its-kronos/The-Breadboard/Kicad/Breadboard.kicad_sch

## KiCad design Kicad/Breadboard.kicad_sch (2025-06-30)

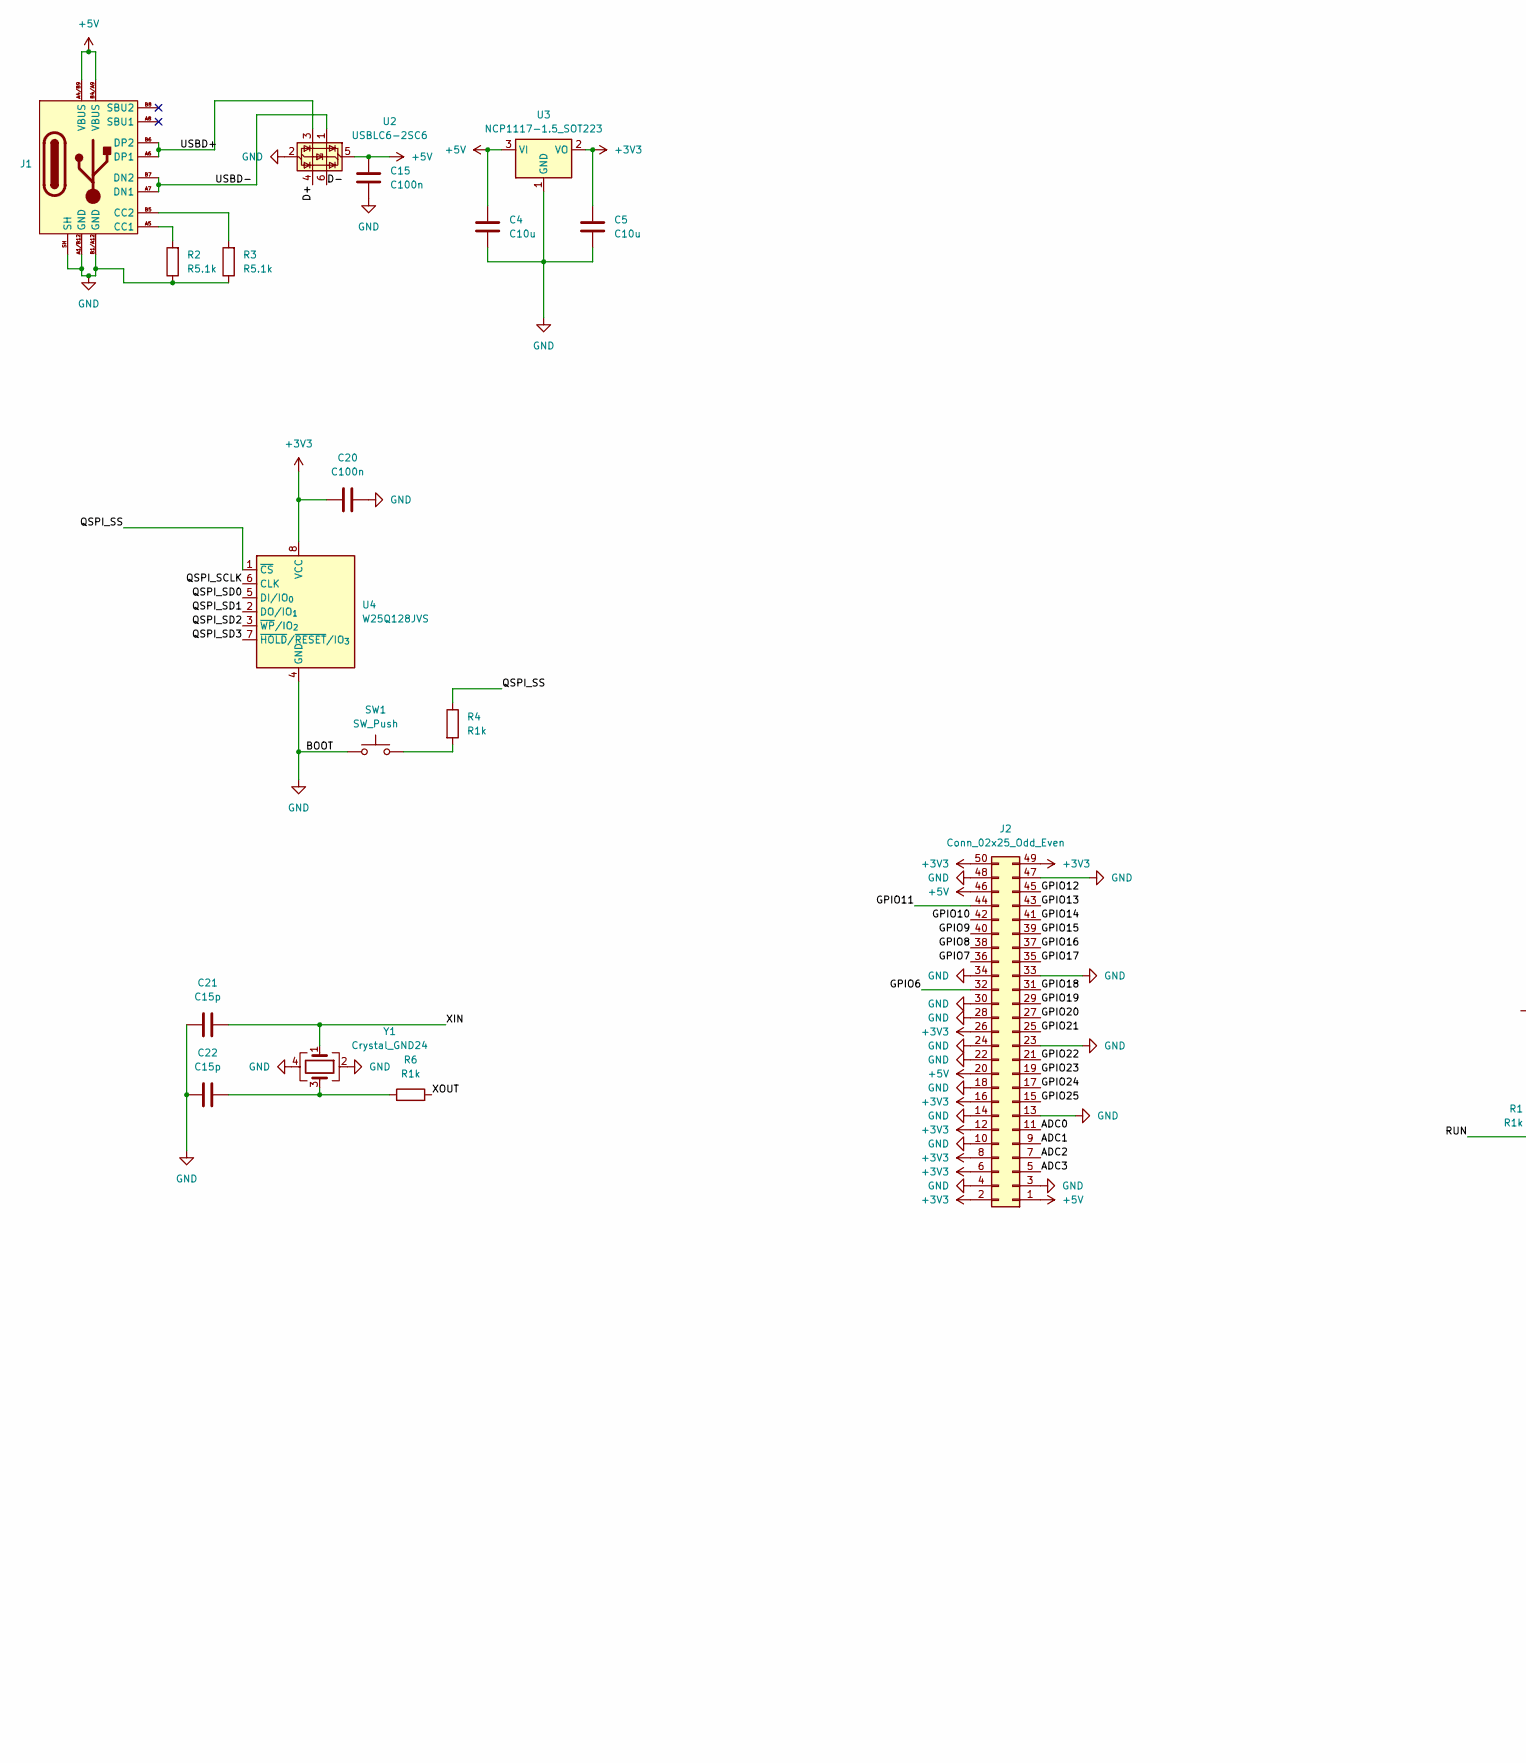
[picture p2: schematic Breadboard.kicad_sch, part in row 1, column 1]

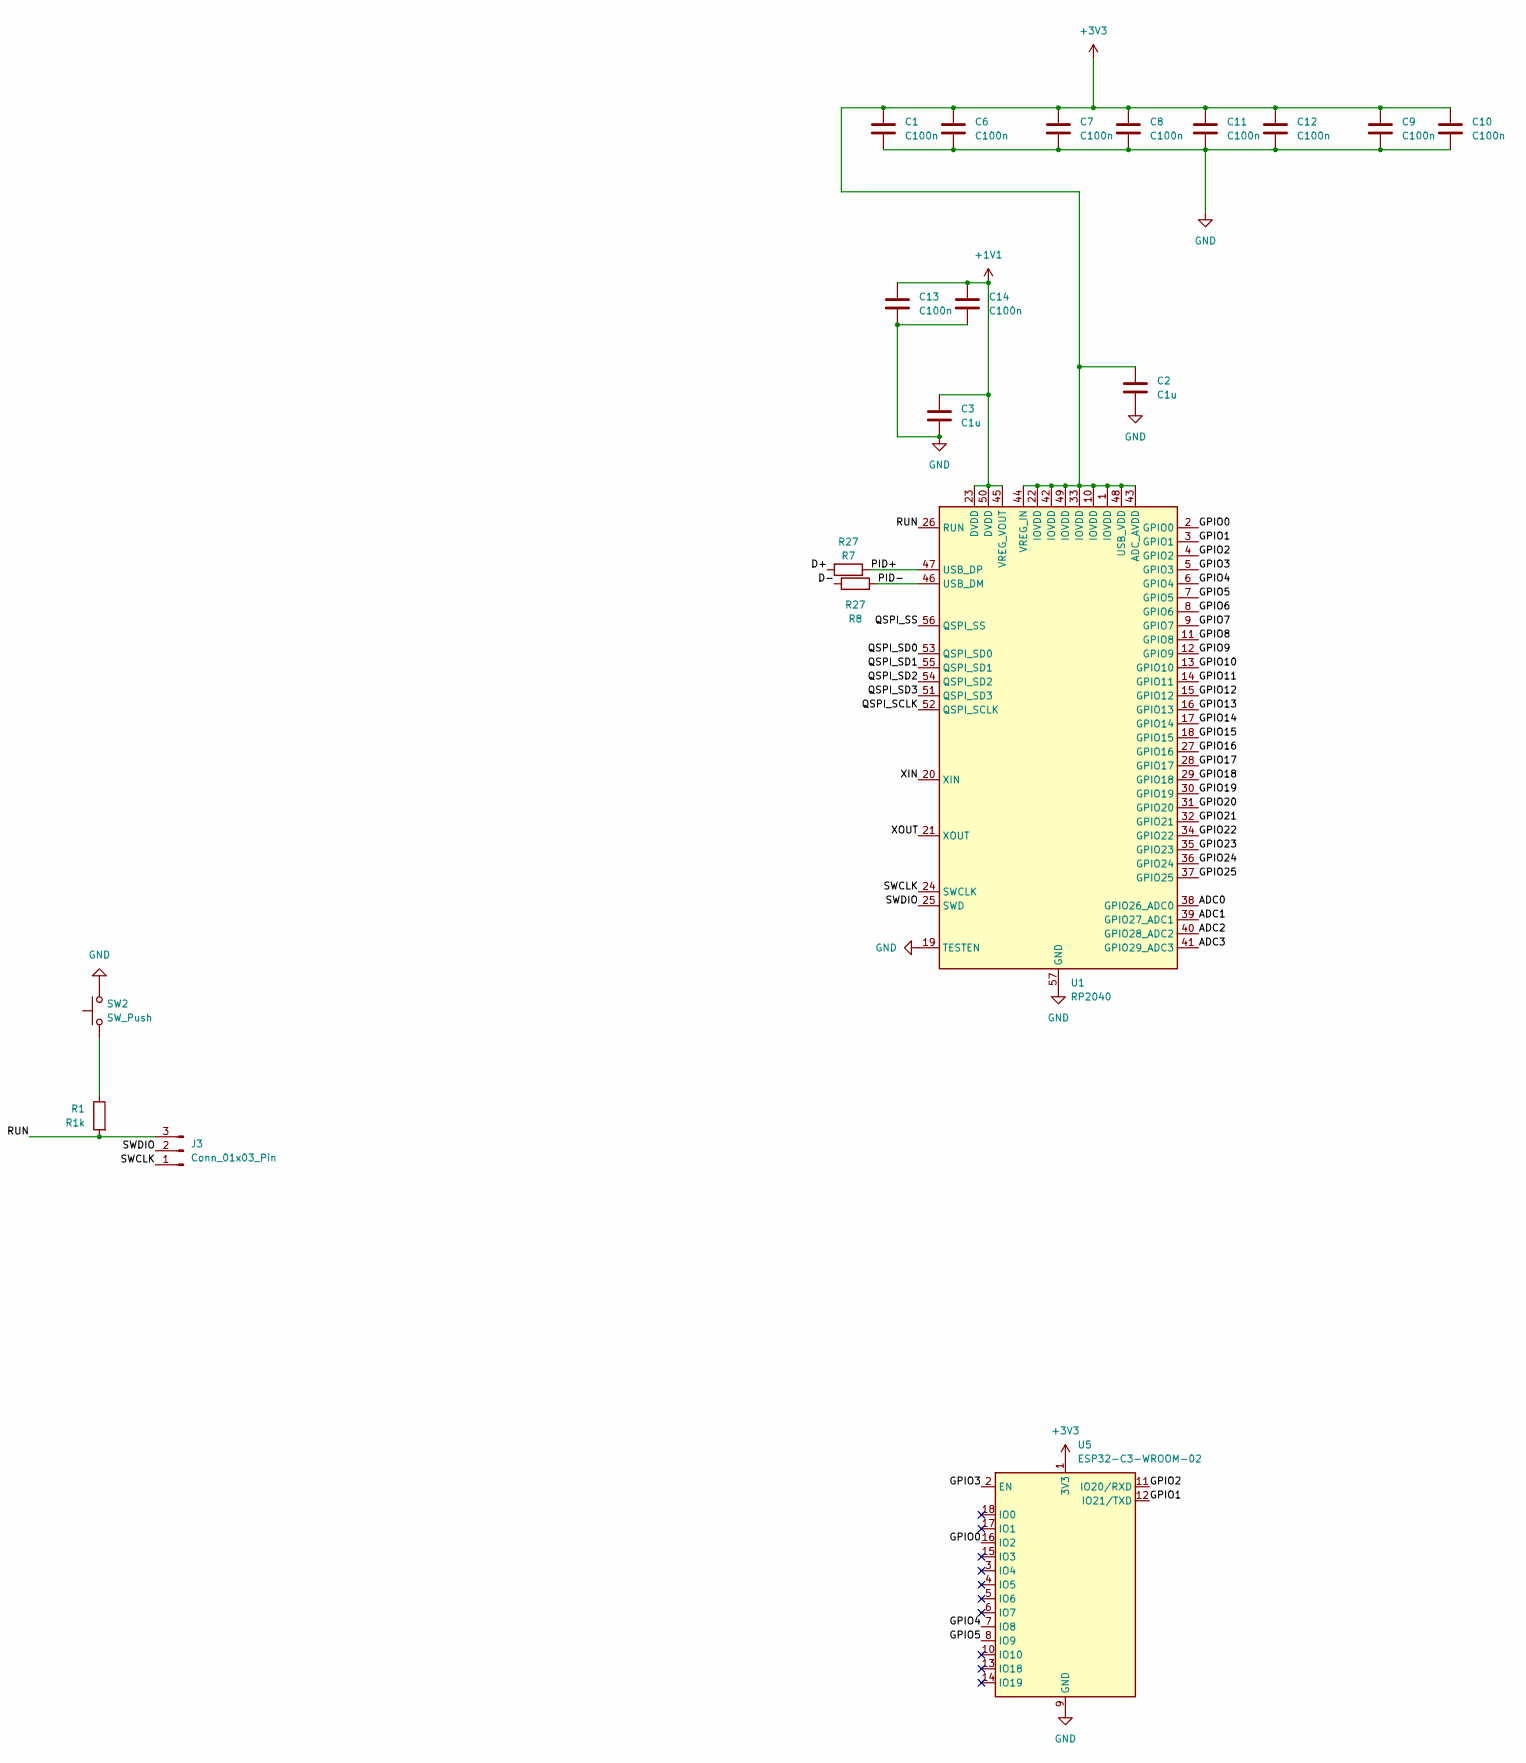
[picture p3: schematic Breadboard.kicad_sch, part in row 1, column 2]

Parts:
C1, C6, C7, C8, C9, C10, C11, C12, C13, C14, C15, C20: C100n; C_0402_1005Metric
C2, C3: C1u; C_0402_1005Metric
C4, C5: C10u; C_0402_1005Metric
C21, C22: C15p; C_0402_1005Metric
J1: Korean Hroparts Elec - Type C 31 M 12 - 16P - USB 2.0
J2: Conn_02x25_Odd_Even; PinHeader_2x25_P1.00mm_Vertical
J3: Conn_01x03_Pin; PinHeader_1x03_P1.00mm_Vertical
R1, R4, R6: R1k; R_0402_1005Metric
R2, R3: R5.1k; R_0402_1005Metric
R7, R8: R27; R_0603_1608Metric
SW1, SW2: SW_Push; SW_PUSH_6mm
U1: RP2040; QFN-56-1EP_7x7mm_P0.4mm_EP3.2x3.2mm
U2: USBLC6-2SC6; SOT-23-6
U3: NCP1117-1.5_SOT223; SOT-223-3_TabPin2
U4: W25Q128JVS; SOIC-8_5.3x5.3mm_P1.27mm
U5: ESP32-C3-WROOM-02
Y1: Crystal_GND24; Crystal_SMD_3225-4Pin_3.2x2.5mm

Connections:
+1V1: C3.1, C13.1, C14.1, U1.23 (DVDD), U1.45 (VREG_VOUT), U1.50 (DVDD)
+3V3: C1.1, C2.1, C5.1, C6.1, C7.1, C8.1, C9.1, C10.1, C11.1, C12.1, C20.1, J2.2, J2.6, J2.8, J2.12, J2.16, J2.26, J2.49, J2.50, U1.1 (IOVDD), U1.10 (IOVDD), U1.22 (IOVDD), U1.33 (IOVDD), U1.42 (IOVDD), U1.43 (ADC_AVDD), U1.44 (VREG_IN), U1.48 (USB_VDD), U1.49 (IOVDD), U3.2 (VO), U4.8 (VCC), U5.1 (3V3)
+5V: C4.1, C15.1, J1.A4/B9 (VBUS), J1.B4/A9 (VBUS), J2.1, J2.20, J2.46, U2.5 (VBUS), U3.3 (VI)
ADC0: J2.11, U1.38 (GPIO26_ADC0)
ADC1: J2.9, U1.39 (GPIO27_ADC1)
ADC2: J2.7, U1.40 (GPIO28_ADC2)
ADC3: J2.5, U1.41 (GPIO29_ADC3)
D+: R7.2, U2.4 (I/O2)
D-: R8.2, U2.6 (I/O1)
GND: C1.2, C2.2, C3.2, C4.2, C5.2, C6.2, C7.2, C8.2, C9.2, C10.2, C11.2, C12.2, C13.2, C14.2, C15.2, C20.2, C21.1, C22.1, J1.A1/B12 (GND), J1.B1/A12 (GND), J1.SH, J2.3, J2.4, J2.10, J2.13, J2.14, J2.18, J2.22, J2.23, J2.24, J2.28, J2.30, J2.33, J2.34, J2.47, J2.48, R2.1, R3.1, SW1.1, SW2.2, U1.19 (TESTEN), U1.57 (GND), U2.2 (GND), U3.1 (GND), U4.4 (GND), U5.9 (GND), U5.19 (GND), Y1.2, Y1.4
GPIO0: U1.2 (GPIO0), U5.16 (IO2)
GPIO1: U1.3 (GPIO1), U5.12 (IO21/TXD)
GPIO2: U1.4 (GPIO2), U5.11 (IO20/RXD)
GPIO3: U1.5 (GPIO3), U5.2 (EN)
GPIO4: U1.6 (GPIO4), U5.7 (IO8)
GPIO5: U1.7 (GPIO5), U5.8 (IO9)
GPIO6: J2.32, U1.8 (GPIO6)
GPIO7: J2.36, U1.9 (GPIO7)
GPIO8: J2.38, U1.11 (GPIO8)
GPIO9: J2.40, U1.12 (GPIO9)
GPIO10: J2.42, U1.13 (GPIO10)
GPIO11: J2.44, U1.14 (GPIO11)
GPIO12: J2.45, U1.15 (GPIO12)
GPIO13: J2.43, U1.16 (GPIO13)
GPIO14: J2.41, U1.17 (GPIO14)
GPIO15: J2.39, U1.18 (GPIO15)
GPIO16: J2.37, U1.27 (GPIO16)
GPIO17: J2.35, U1.28 (GPIO17)
GPIO18: J2.31, U1.29 (GPIO18)
GPIO19: J2.29, U1.30 (GPIO19)
GPIO20: J2.27, U1.31 (GPIO20)
GPIO21: J2.25, U1.32 (GPIO21)
GPIO22: J2.21, U1.34 (GPIO22)
GPIO23: J2.19, U1.35 (GPIO23)
GPIO24: J2.17, U1.36 (GPIO24)
GPIO25: J2.15, U1.37 (GPIO25)
unnamed: C22.2, R6.1, Y1.3
unnamed: J1.A5 (CC1), R2.2
unnamed: J1.B5 (CC2), R3.2
unnamed: R1.1, SW2.1
unnamed: R4.2, SW1.2
PID+: R7.1, U1.47 (USB_DP)
PID-: R8.1, U1.46 (USB_DM)
QSPI_SCLK: U1.52 (QSPI_SCLK), U4.6 (CLK)
QSPI_SD0: U1.53 (QSPI_SD0), U4.5 (DI/IO_{0})
QSPI_SD1: U1.55 (QSPI_SD1), U4.2 (DO/IO_{1})
QSPI_SD2: U1.54 (QSPI_SD2), U4.3 (~WP/IO_{2})
QSPI_SD3: U1.51 (QSPI_SD3), U4.7 (~HOLD/~RESET/IO_{3})
QSPI_SS: R4.1, U1.56 (QSPI_SS), U4.1 (~CS)
RUN: J3.3, R1.2, U1.26 (RUN)
SWCLK: J3.1, U1.24 (SWCLK)
SWDIO: J3.2, U1.25 (SWD)
USBD+: J1.A6 (DP1), J1.B6 (DP2), U2.3 (I/O2)
USBD-: J1.A7 (DN1), J1.B7 (DN2), U2.1 (I/O1)
XIN: C21.2, U1.20 (XIN), Y1.1
XOUT: R6.2, U1.21 (XOUT)
